MandaranK/SmartIrrigationControlSystem/FinalPCB.PNG

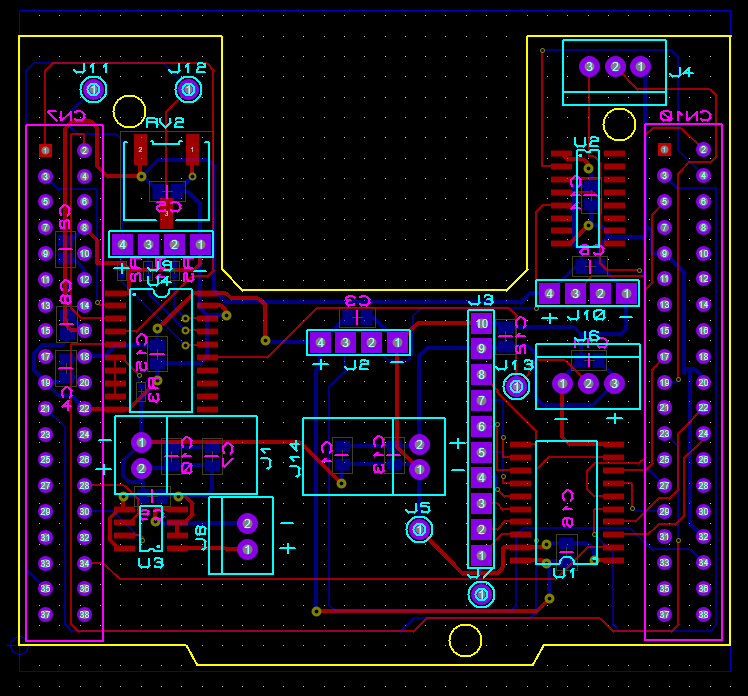
FinalPCB.PNG
