MandaranK/SmartIrrigationControlSystem/Project Design/Images/3D_Model_Bottom.PNG

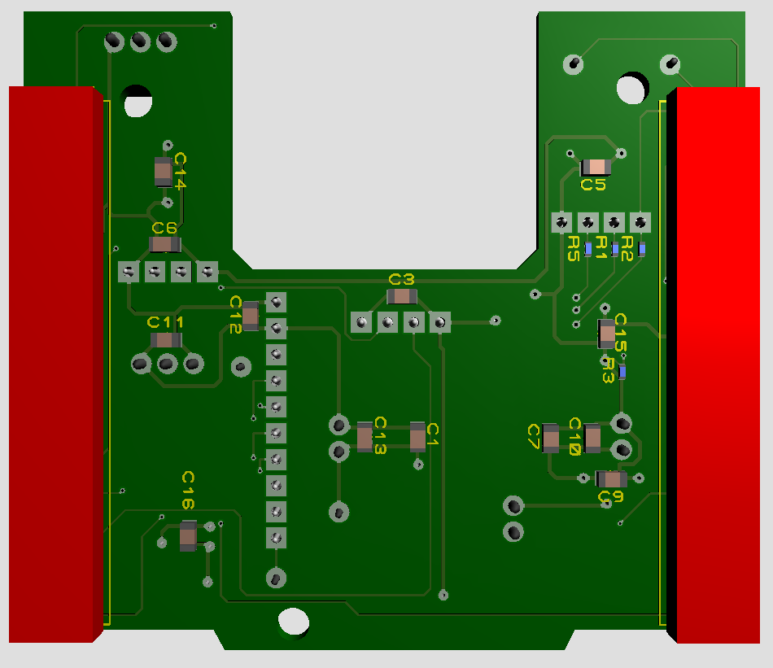
Project Design/Images/3D_Model_Bottom.PNG
