MandaranK/SmartIrrigationControlSystem/Project Design/Images/BottomSilk.PNG

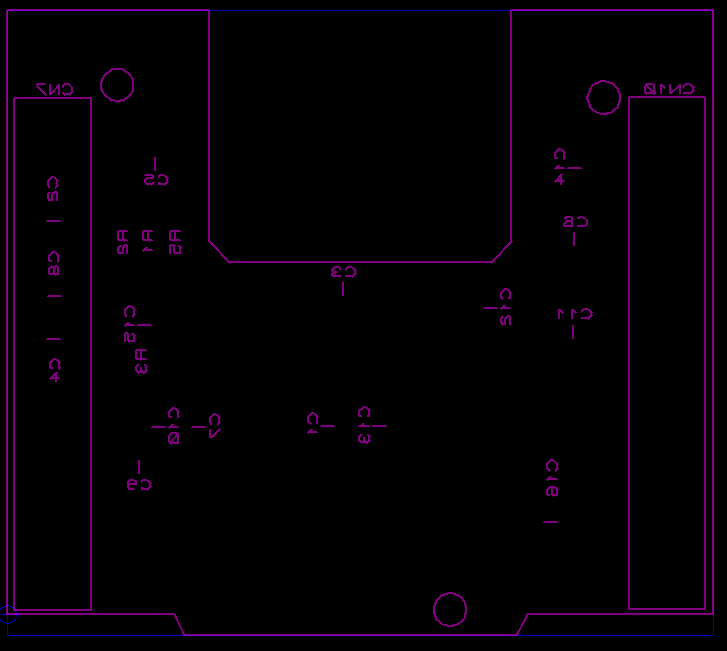
Project Design/Images/BottomSilk.PNG
