MandaranK/SmartIrrigationControlSystem/Project Design/Images/Full.PNG

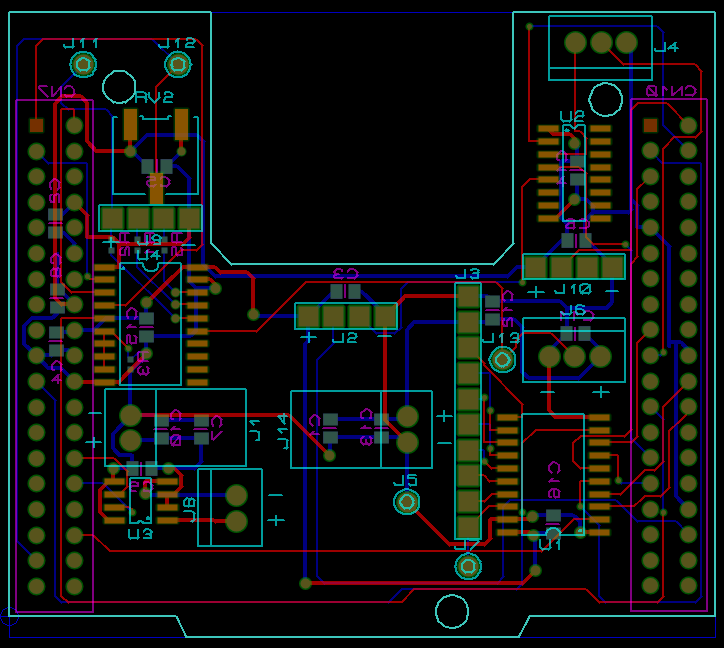
Project Design/Images/Full.PNG
