MandaranK/SmartIrrigationControlSystem/Project Design/Images/TopCopper.PNG

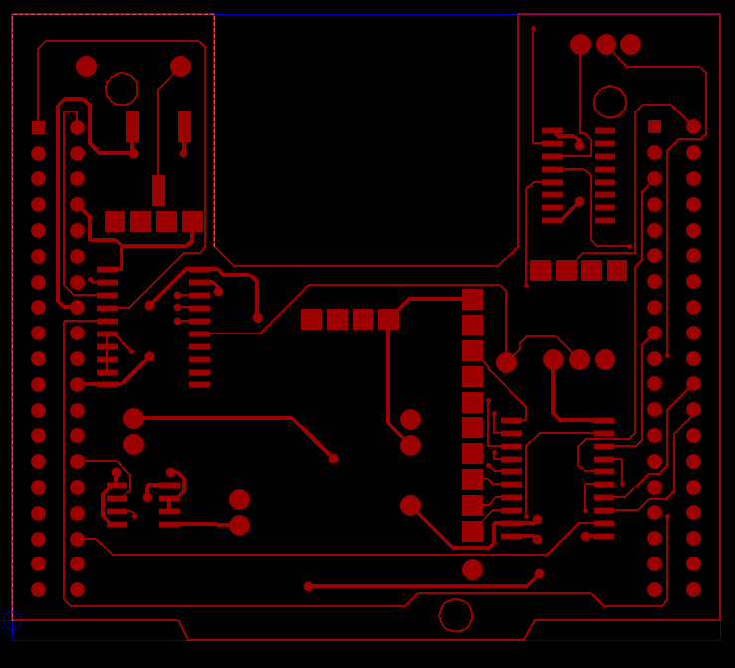
Project Design/Images/TopCopper.PNG
