MandaranK/SmartIrrigationControlSystem/Project Design/Images/TopResist.PNG

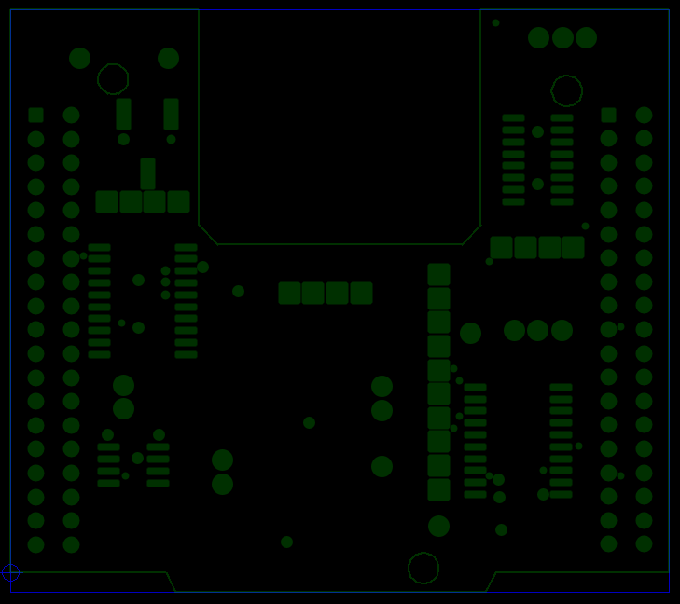
Project Design/Images/TopResist.PNG
